UR3IQO/AngeliaLite/Firmware/FPGA/Led_control.v

//
//  HPSDR - High Performance Software Defined Radio
//
//  Metis code. 
//
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

//  Led_control - Copyright 2009, 2010, 2011  Phil Harman VK6APH
//  April 2019 - changed to use in AngeliaLite by Oleg Skydan UR3IQO


// Led control module

// setting on  		 = high turns the LED on
// setting slow_flash = high flashes the LED once per second 
// setting fast_flash = high flashes the LED 5 times per second
// setting vary       = high flashes the LED fast then slow

// clock is at 25MHz 


module Led_control (clock, on, slow_flash, fast_flash, vary, LED);

input clock;
input on;
input slow_flash;
input fast_flash;
input vary;

output reg LED;

parameter clock_speed = 1;

// calculate timer variables based on clock_speed passed

localparam slow_period = clock_speed/2;		// one flash per second
localparam fast_period = clock_speed/10;		// 5 flashes per second


reg [23:0]counter;
reg [24:0]period;
reg [1:0]swap;

always @ (posedge clock)
begin
		if (on)
			LED <= 0;
		else if (fast_flash) begin
			if (counter == fast_period) begin
				LED <= ~LED;
				counter <= 0;
			end 
			else counter <= counter + 1'b1;
		end 
		else if (slow_flash) begin
			if (counter == slow_period) begin
				LED <= ~LED;
				counter <= 0;
			end 
			else counter <= counter + 1'b1;
		end 
		else if (vary) begin
			if (swap == 0 || swap == 1)
			 period <= slow_period;
			else
			 period <= fast_period;
			if (counter == period) begin
				LED <= ~LED;
				counter <= 0;
				swap <= swap + 1'b1;
			end
			else counter <= counter + 1'b1;
		end
		else LED <= 1'b1;    // LED off 		
end
endmodule
