UR3IQO/AngeliaLite/Firmware/FPGA/High_Priority_CC.v

//-----------------------------------------------------------------------------
//                          High_Priority_CC.v
//-----------------------------------------------------------------------------

//
//  HPSDR - High Performance Software Defined Radio
//
//  
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

//  Copyright 2010, 2011, 2012, 2013, 2014  Phil Harman VK6(A)PH

// ***** need to check sequence error 

/*
	The maximum payload length in a UDP frame is 1444 bytes (without fragmentation).
	We use 4 bytes to hold the sequency number so 1440 bytes are avaialble for data.
	In which case we count the frame from 0 to 1443.
	
	When the code detects that the frame is for the High_Priority_CC port (1027) then the MSB
	of the sequence number is received.  We then read the next 3 bytes to complete the 
	sequence number.  Tt the end of the sequence number the byte_number is 3.
	
	Note that udp_rx_active will drop once the UDP packet has been received. In which case there is 
	no need to detect the end of packet. 
	
	
		 Byte Data
			0	Seq #	[31:24]
			1	Seq #	[23:16]
			2	Seq #	[15:8]
			3	Seq #	[7:0]
			4	Bits  [0] = run, [1] = PTT0…[4] = PTT3
			5	CWX0	[0] = CWX, [1] = Dot, [2] = Dash
			6	CWX1	[0] = CWX, [1] = Dot, [2] = Dash
			7	CWX2	[0] = CWX, [1] = Dot, [2] = Dash
			8	CWX3	[0] = CWX, [1] = Dot, [2] = Dash
			9	RX0 (Hz)/Mercury0 - Rx0	[31:24]
			10									[23:16]
			11									[15:8]
			12									[7:0]
			13	RX1/Mercury0 - Rx1		[31:24]
			14									[23:16]
			15									[15:8]
			16									[7:0]

        345	Tx0 Drive Level			0-255
	
	    1432	Alex 0						[31:24]
		 1433	Alex 0						[23:16]
		 1434	Alex 0						[15:8]
		 1435	Alex 0						[7:0]
		 
       1442	Step Attenuator 1 		(0 - 31dB)
       1443	Step Attenuator 0 		(0 - 31dB)
	
	

*/


module High_Priority_CC 
			( 	
				input clock,
				input [15:0] to_port,
				input udp_rx_active,
				input [7:0] udp_rx_data,
				input HW_timeout,
			   output reg run,
				output reg PC_PTT,
				output reg CWX,
				output reg Dot,
				output reg Dash,
				output reg [31:0]Rx_frequency[0:NR-1] /* ramstyle = "logic" */,		
				output reg [31:0]Tx0_frequency,
				output reg [31:0]Alex_data,
				output reg  [7:0]drive_level,
				output reg  [4:0]Attenuator0,
				output reg  [4:0]Attenuator1,
				output reg  [7:0]Open_Collector,
				output reg  [7:0]User_Outputs,
				output reg  [7:0]Mercury_Attenuator,				
				output reg Alex_data_ready,
				output  HW_reset
			);
			
parameter port = 16'd1027;	
parameter NR;

localparam 
				IDLE = 1'd0,
				PROCESS = 1'd1;
			
reg [31:0] CC_sequence_number;
reg [10:0] byte_number;
reg state;


reg [31:0]temp_frequency;

//Recalculate frequencies
//The original HPSDR operates at 122880000Hz clock
//we use 77760000Hz, so the formula is:
//corrected_freq = freq * 81 / 128
wire [63:0] temp_frequency_cor;

localparam M2 = 25'd26512144;
localparam M3 = 24'd8388608;

assign temp_frequency_cor = temp_frequency * M2 + M3;

reg [31:0]temp_Alex_data;

reg [$clog2(NR):0] j,k;

	
always @(posedge clock)
begin
  if(HW_timeout) run <= 1'b0; 							// reset run if HW timeout 
  
  if (udp_rx_active && to_port == port)				// look for to_port = 1027
    case (state)
      IDLE:	
				begin
				byte_number <= 11'd1;
				Alex_data_ready <= 1'b0;
				CC_sequence_number <= {CC_sequence_number[31-8:0], udp_rx_data};  //save MSB of sequence number
				state <= PROCESS;
				end 
			
		PROCESS:
			begin
				case (byte_number) 	//save balance of sequence number
				  1,2,3: begin
							Alex_data_ready <= 1'b0;
						//	HW_reset <= 1'b1;						
							CC_sequence_number <= {CC_sequence_number[31-8:0], udp_rx_data};
							end
				      4: begin 
							run <= udp_rx_data[0];
							PC_PTT <= udp_rx_data[1];
							end
						5: begin
							CWX  <= udp_rx_data[0];
							Dot  <= udp_rx_data[1]; 
							Dash <= udp_rx_data[2]; 
						   end
				//	endcase

//					for (k = 0, j = 0; j < NR ; k = k + 4, j = j + 1)
//					begin 
//						
//						case (byte_number)
//						 k + 9  : begin 
//                              RX_frequency[j-1] <= temp_frequency_cor[55:24];
//                              temp_frequency[31:24] <= udp_rx_data; 
//                            end  
//						 k + 10 : temp_frequency[23:16] <= udp_rx_data;
//						 k + 11 : temp_frequency[15:8]  <= udp_rx_data;
//						 k + 12 : temp_frequency[7:0]   <= udp_rx_data;
//						endcase
//
//					end

				//		case (byte_number)	

						    9: temp_frequency[31:24] <= udp_rx_data; 
						   10: temp_frequency[23:16] <= udp_rx_data;
						   11: temp_frequency[15:8]  <= udp_rx_data;
						   12: temp_frequency[7:0]   <= udp_rx_data;
					      
                     13: begin 
                            Rx_frequency[0] <= temp_frequency_cor[55:24];
                            temp_frequency[31:24] <= udp_rx_data; 
                       end  
						   14: temp_frequency[23:16] <= udp_rx_data;
						   15: temp_frequency[15:8]  <= udp_rx_data;
						   16: temp_frequency[7:0]   <= udp_rx_data;

						   17: begin 
                           Rx_frequency[1] <= temp_frequency_cor[55:24];
                           temp_frequency[31:24] <= udp_rx_data; 
                       end  
						   18: temp_frequency[23:16] <= udp_rx_data;
						   19: temp_frequency[15:8]  <= udp_rx_data;
						   20: temp_frequency[7:0]   <= udp_rx_data;
					      
                     21: begin 
                            Rx_frequency[2] <= temp_frequency_cor[55:24];
                            temp_frequency[31:24] <= udp_rx_data; 
                       end  
						   22: temp_frequency[23:16] <= udp_rx_data;
						   23: temp_frequency[15:8]  <= udp_rx_data;
						   24: temp_frequency[7:0]   <= udp_rx_data;

						   25: begin 
                           Rx_frequency[3] <= temp_frequency_cor[55:24];
                       //    temp_frequency[31:24] <= udp_rx_data; 
                       end  
				
/*							9: temp_frequency0 [31:24] <= udp_rx_data; 
						  10: temp_frequency0 [23:16] <= udp_rx_data;
						  11: temp_frequency0 [15:8]  <= udp_rx_data;
						  12: temp_frequency0 [7:0]   <= udp_rx_data; 

						  13: temp_frequency1 [31:24] <= udp_rx_data; 
						  14: temp_frequency1 [23:16] <= udp_rx_data;
						  15: temp_frequency1 [15:8]  <= udp_rx_data;
						  16: temp_frequency1 [7:0]   <= udp_rx_data; 
						  
						  17: temp_frequency2 [31:24] <= udp_rx_data; 					  
						  18: temp_frequency2 [23:16] <= udp_rx_data;
						  19: temp_frequency2 [15:8]  <= udp_rx_data;
						  20: temp_frequency2 [7:0]   <= udp_rx_data; 				  

						  21: temp_frequency3 [31:24] <= udp_rx_data; 
						  22: temp_frequency3 [23:16] <= udp_rx_data;
						  23: temp_frequency3 [15:8]  <= udp_rx_data;
						  24: temp_frequency3 [7:0]   <= udp_rx_data; 

						  25: temp_frequency4 [31:24] <= udp_rx_data; 
						  26: temp_frequency4 [23:16] <= udp_rx_data;
						  27: temp_frequency4 [15:8]  <= udp_rx_data;
						  28: temp_frequency4 [7:0]   <= udp_rx_data; 
	
						  29: temp_frequency5 [31:24] <= udp_rx_data; 
						  30: temp_frequency5 [23:16] <= udp_rx_data;
						  31: temp_frequency5 [15:8]  <= udp_rx_data;
						  32: temp_frequency5 [7:0]   <= udp_rx_data; 	

						  33: temp_frequency6 [31:24] <= udp_rx_data; 
						  34: temp_frequency6 [23:16] <= udp_rx_data;
						  35: temp_frequency6 [15:8]  <= udp_rx_data;
						  36: temp_frequency6 [7:0]   <= udp_rx_data; 						  
*/

						 329:	temp_frequency [31:24]  <= udp_rx_data;
						 330:	temp_frequency [23:16]  <= udp_rx_data;					
						 331:	temp_frequency [15:8]   <= udp_rx_data;
						 332:	temp_frequency [7:0]    <= udp_rx_data;	
                   333: Tx0_frequency <= temp_frequency_cor[56:25]; //divide frequency phase by 2 for TX cause
                                                                       //DAC clock is two times the ADC clock


						 345: drive_level <= udp_rx_data;
						 
						 350: begin
								// Rx_frequency[0] <= temp_frequency0_cor[55:24]; 
								// Rx_frequency[1] <= temp_frequency1_cor[55:24];
/*								Rx_frequency[2] <= temp_frequency2;					
								Rx_frequency[3] <= temp_frequency3;		

								Rx_frequency[4] <= temp_frequency4;
								Rx_frequency[5] <= temp_frequency5;
								Rx_frequency[6] <= temp_frequency6;
*/
								end
		
						1401:	Open_Collector 		  <=  udp_rx_data;
						1402:	User_Outputs 			  <=  udp_rx_data;
						1403:	Mercury_Attenuator     <=  udp_rx_data;	
						
						1432:	temp_Alex_data [31:24]      <= udp_rx_data;
						1433:	temp_Alex_data [23:16]      <= udp_rx_data;					
						1434:	temp_Alex_data [15:8]       <= udp_rx_data;
						1435:	temp_Alex_data [7:0]        <= udp_rx_data;	
		
						1437:	Alex_data <= temp_Alex_data;
		
						1442: begin 
									Attenuator1 <= udp_rx_data[4:0];
									Alex_data_ready <= 1'b1;
								end 
						1443: begin 
									Attenuator0 <= udp_rx_data[4:0]; 
									Alex_data_ready <= 1'b0;
									//HW_reset <= 1'b0;
								end
										  
			   default: if (byte_number > 11'd1443) state <= IDLE;  
			   endcase  
		  
				byte_number <= byte_number + 11'd1;
			end
		default: state <= IDLE;
		endcase 
	else state <= IDLE;	

end		
		
// inhibit HW_reset if Ethernet data stops 
assign HW_reset = (byte_number > 4  && udp_rx_active);	
	
endmodule			
