UR3IQO/AngeliaLite/Firmware/FPGA/audio_I2S.v

// audio_I2S.v

//
//  HPSDR - High Performance Software Defined Radio
//
//  Angelia code. 
//
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
// (C) Phil Harman VK6PH - 2014 

/*

		LRCLK    ---------------+													   +-----------------------------------------+
										|													   |														|
										+-----------------------------------------+														+-----

		BCLK      --+  +--+  +--+  +--+  +--+  +--+  +--+  +--+  +--+  +--+  +--+  +--+  +--+  +--+  +--+  +--+  +--+  +--+
					   |  |  |  |  |  |  |  |  |  |  |  |  |  |  |  |  |  |  |  |  |  |  |  |  |  |  |  |  |  |  |  |  |  |  |
					   +--+  +--+  +--+  +--+  +--+  +  +  +--+  +--+  +  +  +--+  +--+  +--+  +  +  +--+  +--+  +  +  +--+  +--

		DIN       --------------------+-----+-----+-- --+-----+-----+ --    ----+-----+-- --+-----+-----+-----+------
		(data bit)							| 31  | 30  |  // |  17 |  16 |  15 //    | 15  | 14  |     |  1  |  0  |
					 --------------------+-----+-----+-- --+-----+-----+ --    ----+-----+-----+-- --+-----+-----+------
												<-----------  left channel ---------------><----------- right channel --------------> 
												
								+-----+																										+-----+
								|	   |																										|     |
		get_data	---------+		+-----------------------------------------------------------------------------+	   +-----------------  				
												
												
												
		TLV320 is in slave, I2S mode.
		
		NOTE:  BCLK in PLL_IF is set at 180 degrees so that LRCLK changes on negative edge to comply with I2S format 					 
					 
*/

module audio_I2S 
	( 
		input [31:0]data_in,
		input [11:0]rdusedw,
		input run,
		input empty,
		input BCLK,
		input LRCLK,
		output get_data,
		output reg data_out	
	);
	
	
reg [31:0] data_in_tmp;
reg [4:0] state;
reg [4:0] data_count;
reg [15:0] ramp_count;
reg [1:0] ramp_dir = 0; // 0=stay_quiet 1=stay_even 2=ramp up 3=ramp down
reg holdoff;
reg shift = 0;

always @ (posedge LRCLK)
begin 
	// below is an attempt to prevent pops/clicks occurring as a result of
	// the audio fifo temporarily going empty, ramps are ~ 5.33ms
	if (!run) begin
		ramp_dir <= 2'd0;
		ramp_count <= 15'd0;
		data_in_tmp <= 32'd0;
		holdoff <= 1'd1;
	end
	// low water reached, start ramping down
	else if (rdusedw < 12'd260 && ramp_dir == 2'd1) begin
		ramp_dir <= 2'd3;
		ramp_count <= 15'd1;
		data_in_tmp <= data_in;
	end
	// high water reached, start ramping back up
	else if (rdusedw > 12'd1788 && ramp_dir == 2'd0) begin
		ramp_dir <= 2'd2;
		ramp_count <= 15'd256; // ramp time is 256/48000 or 5.33ms
		data_in_tmp <= 32'd0;
		holdoff <= 1'd0;
	end
	// ramp up, sample - (from 32767 to 255) * sign, or 0 if sample < ramp value
	// note that if the sample is negative then it adds the ramp value
	else if (ramp_dir == 2'd2) begin
		data_in_tmp <= {(data_in[30:16] > ((ramp_count<<7)-1)) ?
			($signed(data_in[31:16]) - $signed(((ramp_count<<7)-1)*(data_in[31])?-1:1)) : 16'd0,
				(data_in[14:0] > ((ramp_count<<7)-1)) ?
			($signed(data_in[15:0]) - $signed(((ramp_count<<7)-1)*(data_in[15])?-1:1)) : 16'd0};
		if (ramp_count == 15'd1) ramp_dir <= 1; // now stay even
		ramp_count <= ramp_count - 15'd1;
	end
	// ramp down, sample - (from 255 to 32767) * sign, or 0 if sample < ramp value
	else if (ramp_dir == 2'd3) begin
		data_in_tmp <= {(data_in[30:16] > ((ramp_count<<7)-1)) ?
			($signed(data_in[31:16]) - $signed(((ramp_count<<7)-1)*(data_in[31])?-1:1)) : 16'd0,
				(data_in[14:0] > ((ramp_count<<7)-1)) ?
			($signed(data_in[15:0]) - $signed(((ramp_count<<7)-1)*(data_in[15])?-1:1)) : 16'd0};
		if (ramp_count == 15'd256) begin
			ramp_dir <= 0; // now stay quiet
			holdoff <= 1'd1;
		end
		ramp_count <= ramp_count + 15'd1;
	end
	// things are stable at silent or even level playing
	else if (ramp_dir == 2'd0) data_in_tmp <= 32'd0; // quiet
	else data_in_tmp <= data_in; // even
end

always @ (posedge BCLK)
begin 
	if(!empty)		// only run code if fifo has data available
	begin
		case (state)

		0:	begin
				if (LRCLK) state <= 1;		// loop until LRCLK is high
			end 
			
		1:  begin 
				if (!LRCLK) begin 		// loop until LRCLK is low
					shift <= 1;
					data_count <= 5'd31;
					state <= 2;
				end
			end
			
		2: begin
				if (data_count == 16) begin 
					shift <= 0;
					if(LRCLK) begin 
						data_count <= 15;
						shift <= 1;
						state <= 3;
					end 			
				end 
				else begin
					data_count <= data_count - 5'd1;
				end
			end
			
		3:	begin 
				if (data_count == 0) begin
					shift <= 0;
					state <= 0;
				end
				else data_count <= data_count - 5'd1;
			end 
			
		default: state <= 0;
		endcase
	end 
end 

// clock data out on negedge of BCLK so it can be read on postive edge by TLV320	
// request data just before falling edge of LRCLK 
reg [5:0] get_count;		
always @ (negedge BCLK)
begin 
		if (shift) data_out <= data_in_tmp[data_count];
		else data_out <= 0;
		if (!LRCLK) get_count <= 0;
		else get_count <= get_count + 6'd1;
end 
			
assign get_data = ((get_count == 6'd30) && !holdoff); // if holding off, let fifo fill up
			
			
endmodule
	
