UR3IQO/AngeliaLite/Firmware/FPGA/NCO/nco2.v

`timescale 1us/1ns

module nco2 (
  state,
  clk_2x,
  rst,
  phi0,
  phi1,
  cos,
  sin,
);

input             state;
input             clk_2x;
input             rst;
input     [31:0]  phi0;
input     [31:0]  phi1;
output    [18:0]  sin;
output    [18:0]  cos;

logic [31:0]      angle0 = 32'h00;
logic [31:0]      angle1 = 32'h00;

parameter         CALCTYPE = 1;


always @(posedge clk_2x) begin
  if (rst) begin 
    angle0 <= 32'h00;
    angle1 <= 32'h00;
  end else begin
    angle1 <= angle0 + (state ? phi1 : phi0);
    angle0 <= angle1;
  end
end


sincos #(.CALCTYPE(CALCTYPE)) sincos_i (
  .clk(clk_2x),
  .angle(angle1[31:12]),
  .cos(cos),
  .sin(sin)
);

endmodule 
